darknrgy/rudderpedals/Images/Pedal Shaft.png

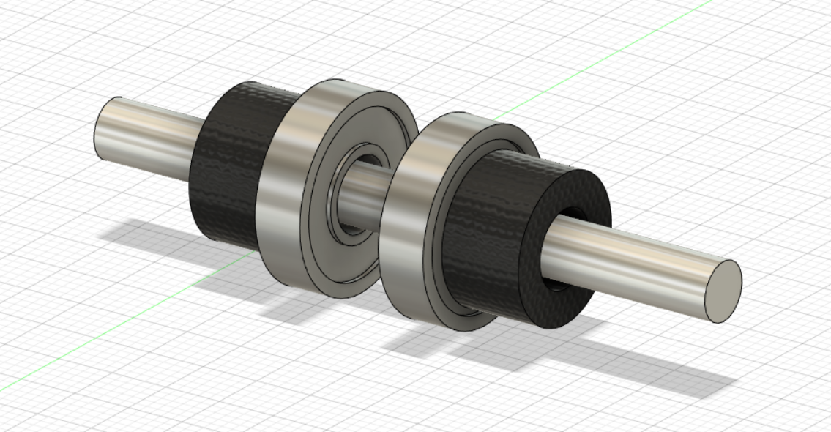
Images/Pedal Shaft.png
