darknrgy/rudderpedals/Images/Rail Shaft.png

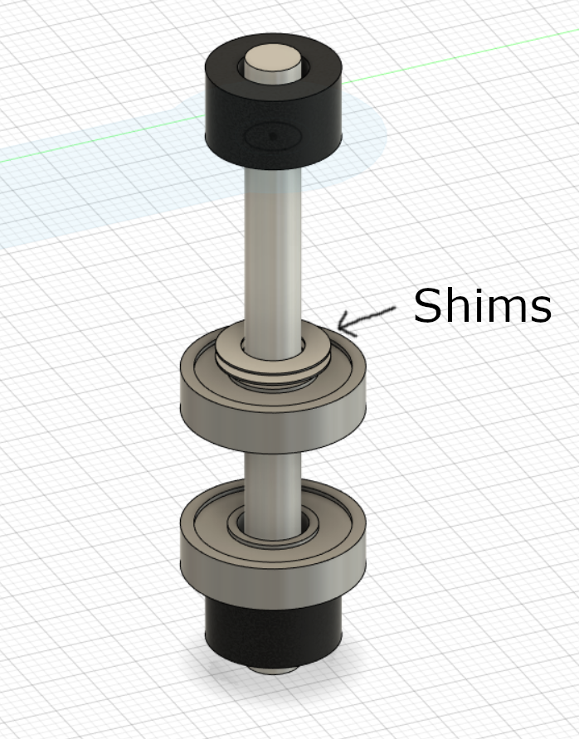
Images/Rail Shaft.png
