darknrgy/rudderpedals/Images/Rudder Pedals.png

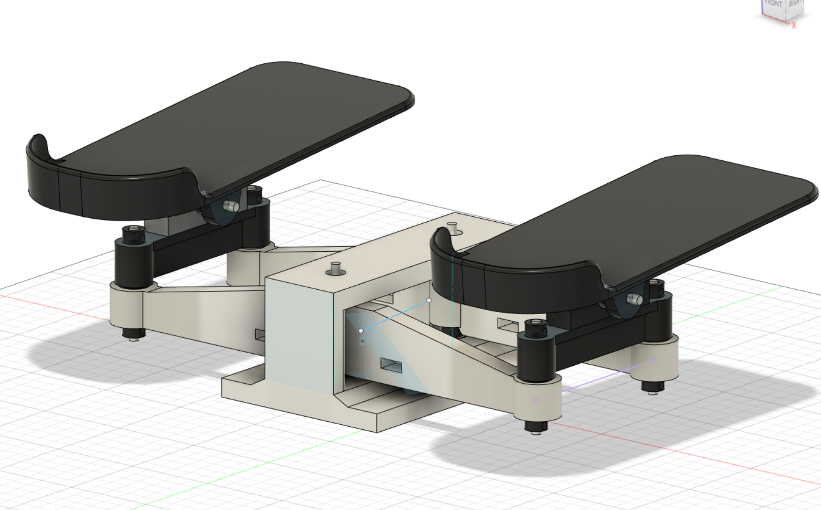
Images/Rudder Pedals.png
